SebKuzminsky/radio-toy/rust/src/command_parser.rs

const BUF_SIZE: usize = 64;

#[derive(Debug)]
pub enum Command {
    Ping,
    Idle,
    TxPreambleBytes(u8),
    SyncWordMSB(u8),
    SyncWordLSB(u8),
    SyncMode(u8),
    Frequency(u32),
    Baud(u32),
    PacketLength(u8),
    TxFifo(u8),
    DoTx,
}

pub struct Parser {
    buf: [u8; BUF_SIZE],
    index: usize,
}

impl Parser {
    pub const fn new() -> Self {
        Self {
            buf: [0; BUF_SIZE],
            index: 0,
        }
    }

    pub fn ingest(&mut self, b: u8) -> Option<Command> {
        match b {
            b'\n' | b'\r' => {
                let r = self.handle_line();
                self.index = 0;
                r
            }

            b => {
                let i = self.index;
                self.buf[i] = b;
                self.index += 1;
                if self.index >= BUF_SIZE {
                    log::info!("input buffer overflow, resetting: {:?}", self.buf);
                    self.index = 0;
                }
                None
            }
        }
    }

    fn handle_line(&self) -> Option<Command> {
        let s = match core::str::from_utf8(&self.buf[0..self.index]) {
            Ok(s) => s,
            Err(_) => return None,
        };

        let mut tokens = s.split_whitespace();
        let cmd = match tokens.next() {
            Some(cmd) => cmd,
            None => return None,
        };

        match cmd {
            cmd if "bootloader".eq_ignore_ascii_case(cmd) => {
                log::info!("resetting to bootloader");
                embassy_rp::rom_data::reset_to_usb_boot(0, 0);
                unreachable!();
            }

            cmd if "ping".eq_ignore_ascii_case(cmd) => {
                log::info!("pong");
                Some(Command::Ping)
            }

            cmd if "idle".eq_ignore_ascii_case(cmd) => Some(Command::Idle),

            cmd if "do-tx".eq_ignore_ascii_case(cmd) => Some(Command::DoTx),

            cmd if "tx-fifo".eq_ignore_ascii_case(cmd) => match tokens.next() {
                Some(t) => match u8::from_str_radix(t, 16) {
                    Ok(byte) => Some(Command::TxFifo(byte)),
                    Err(e) => {
                        log::error!("failed to parse byte from {}: {}", t, e);
                        None
                    }
                },
                None => None,
            },

            cmd if "tx-preamble-bytes".eq_ignore_ascii_case(cmd) => match tokens.next() {
                Some(t) => match t.parse::<u8>() {
                    Ok(num_bytes) => Some(Command::TxPreambleBytes(num_bytes)),
                    Err(e) => {
                        log::error!("failed to parse number from {}: {}", t, e);
                        None
                    }
                },
                None => None,
            },

            cmd if "sync-word-msb".eq_ignore_ascii_case(cmd) => match tokens.next() {
                Some(t) => match t.parse::<u8>() {
                    Ok(n) => Some(Command::SyncWordMSB(n)),
                    Err(e) => {
                        log::error!("failed to parse number from {}: {}", t, e);
                        None
                    }
                },
                None => None,
            },

            cmd if "sync-word-lsb".eq_ignore_ascii_case(cmd) => match tokens.next() {
                Some(t) => match t.parse::<u8>() {
                    Ok(n) => Some(Command::SyncWordLSB(n)),
                    Err(e) => {
                        log::error!("failed to parse number from {}: {}", t, e);
                        None
                    }
                },
                None => None,
            },

            cmd if "sync-mode".eq_ignore_ascii_case(cmd) => match tokens.next() {
                Some(t) => match t.parse::<u8>() {
                    Ok(n) => Some(Command::SyncMode(n)),
                    Err(e) => {
                        log::error!("failed to parse number from {}: {}", t, e);
                        None
                    }
                },
                None => None,
            },

            cmd if "freq".eq_ignore_ascii_case(cmd) => match tokens.next() {
                Some(t) => match t.parse::<u32>() {
                    Ok(n) => Some(Command::Frequency(n)),
                    Err(e) => {
                        log::error!("failed to parse number from {}: {}", t, e);
                        None
                    }
                },
                None => None,
            },

            cmd if "baud".eq_ignore_ascii_case(cmd) => match tokens.next() {
                Some(t) => match t.parse::<u32>() {
                    Ok(n) => Some(Command::Baud(n)),
                    Err(e) => {
                        log::error!("failed to parse number from {}: {}", t, e);
                        None
                    }
                },
                None => None,
            },

            cmd if "pktlen".eq_ignore_ascii_case(cmd) => match tokens.next() {
                Some(t) => match t.parse::<u8>() {
                    Ok(n) => Some(Command::PacketLength(n)),
                    Err(e) => {
                        log::error!("failed to parse number from {}: {}", t, e);
                        None
                    }
                },
                None => None,
            },

            _ => {
                log::info!("unknown command '{}'", cmd);
                None
            }
        }
    }
}
